Mark-MDO47/GraduationCap2017/Buttons/images/71s4Z-NuidL._SL1500_.jpg

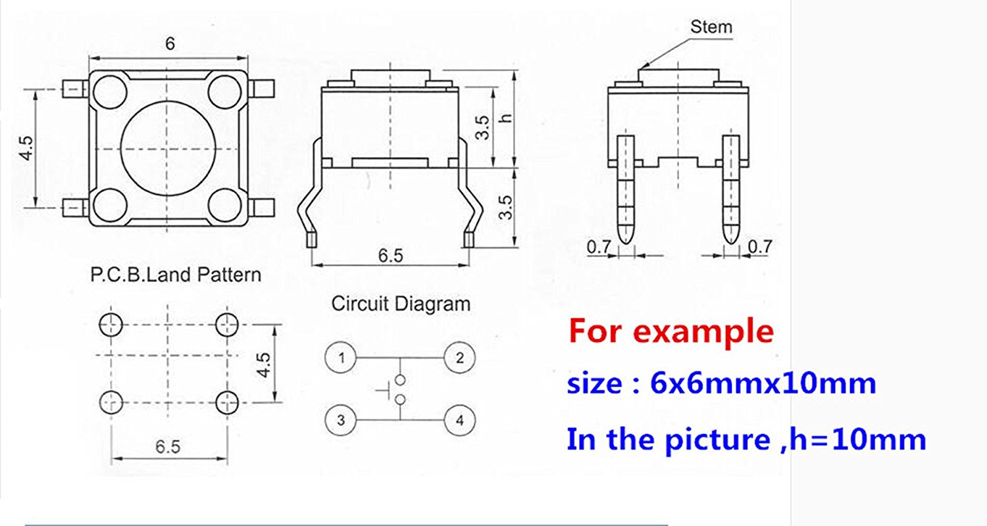
Buttons/images/71s4Z-NuidL._SL1500_.jpg
