Mark-MDO47/GraduationCap2017/FirstCap/GradCapWithDisks_FirstAttempt.JPG

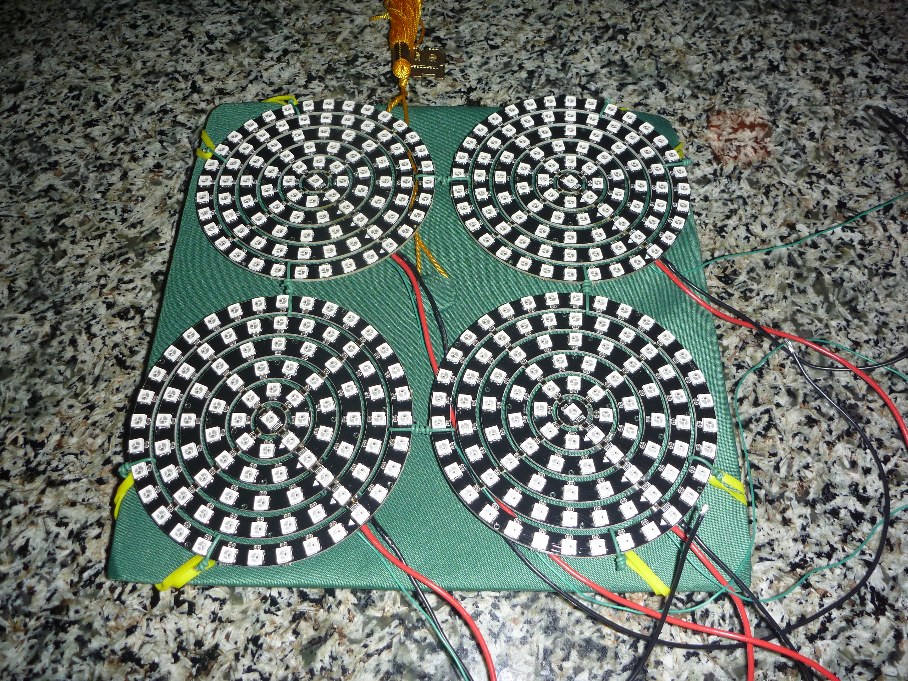
FirstCap/GradCapWithDisks_FirstAttempt.JPG
