Mark-MDO47/GraduationCap2017/FirstCap/P1010498.JPG

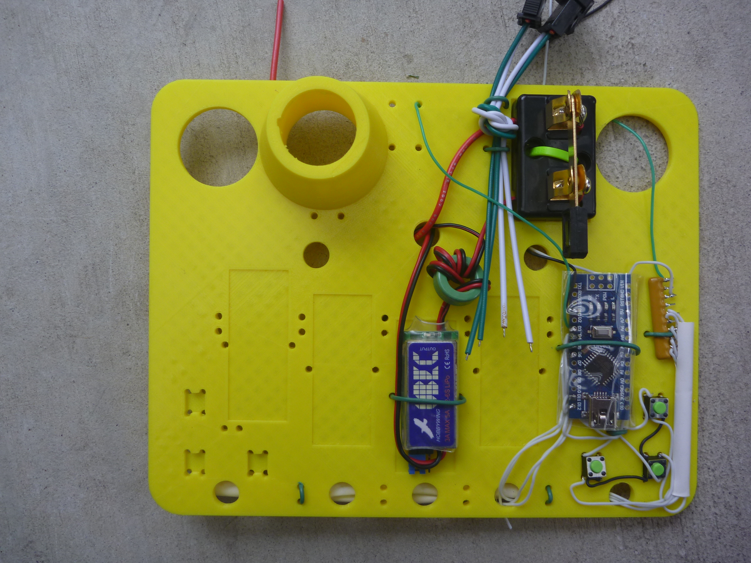
FirstCap/P1010498.JPG
