Mark-MDO47/GraduationCap2017/FirstCap/P1010499.JPG

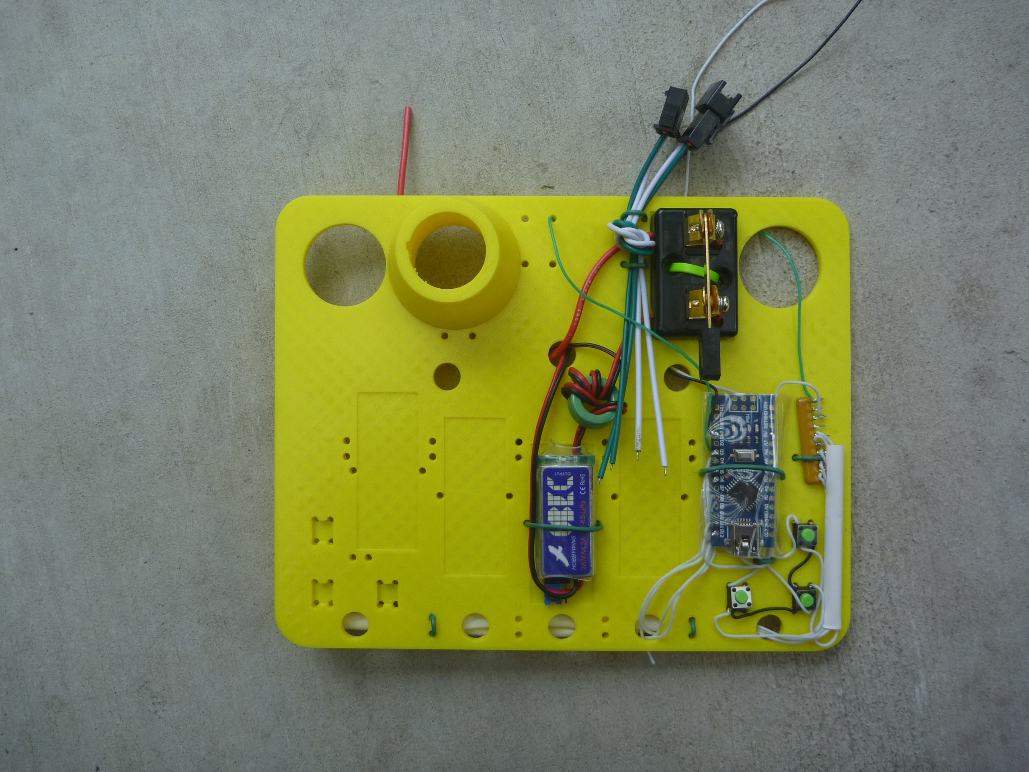
FirstCap/P1010499.JPG
