Mark-MDO47/GraduationCap2017/FirstCap/P1010500.JPG

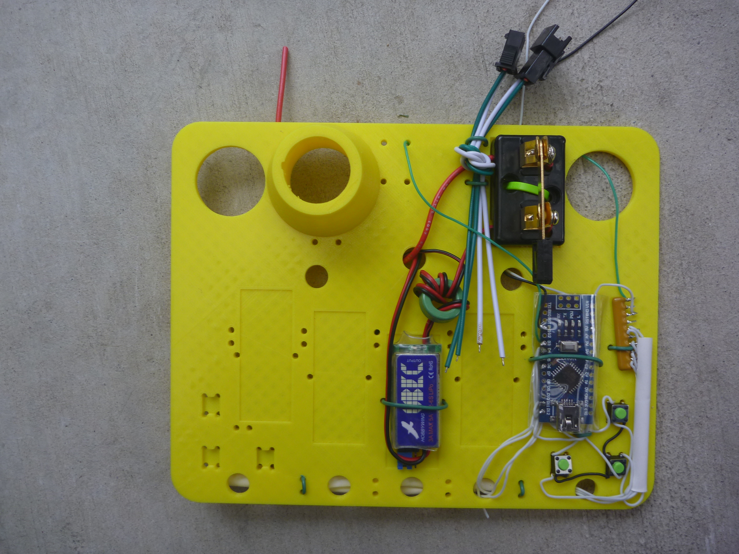
FirstCap/P1010500.JPG
