Mark-MDO47/GraduationCap2017/FirstCap/P1010501.JPG

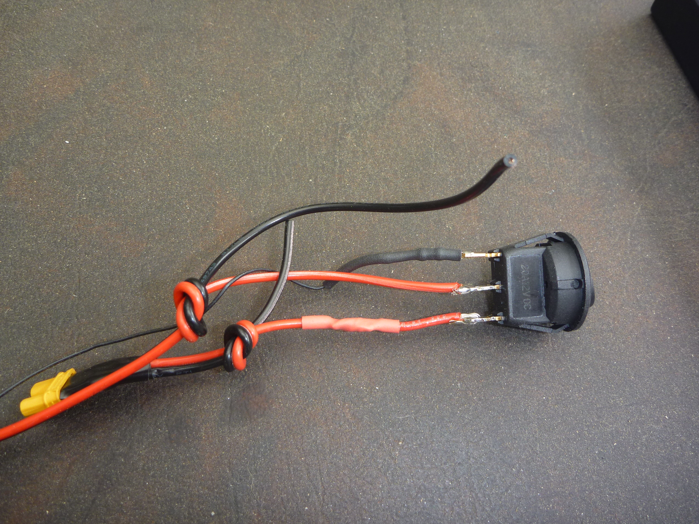
FirstCap/P1010501.JPG
