Mark-MDO47/GraduationCap2017/FirstCap/P1010502.JPG

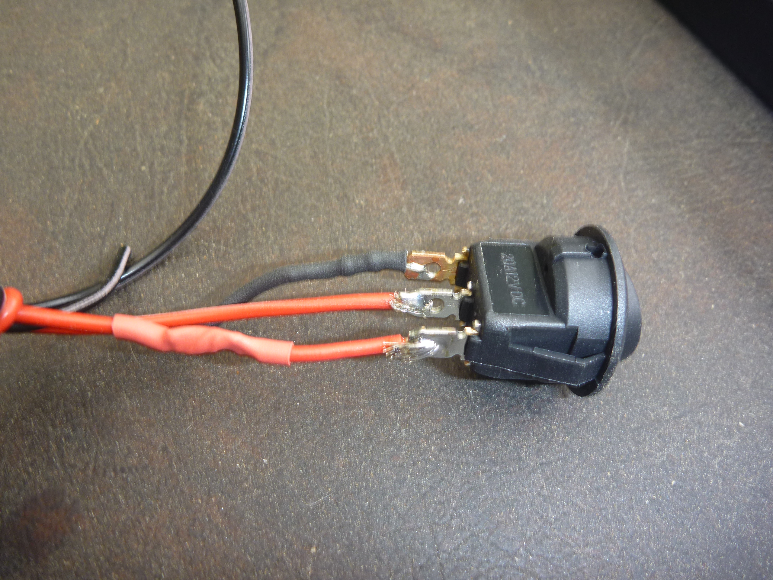
FirstCap/P1010502.JPG
