Mark-MDO47/GraduationCap2017/FirstCap/P1010503.JPG

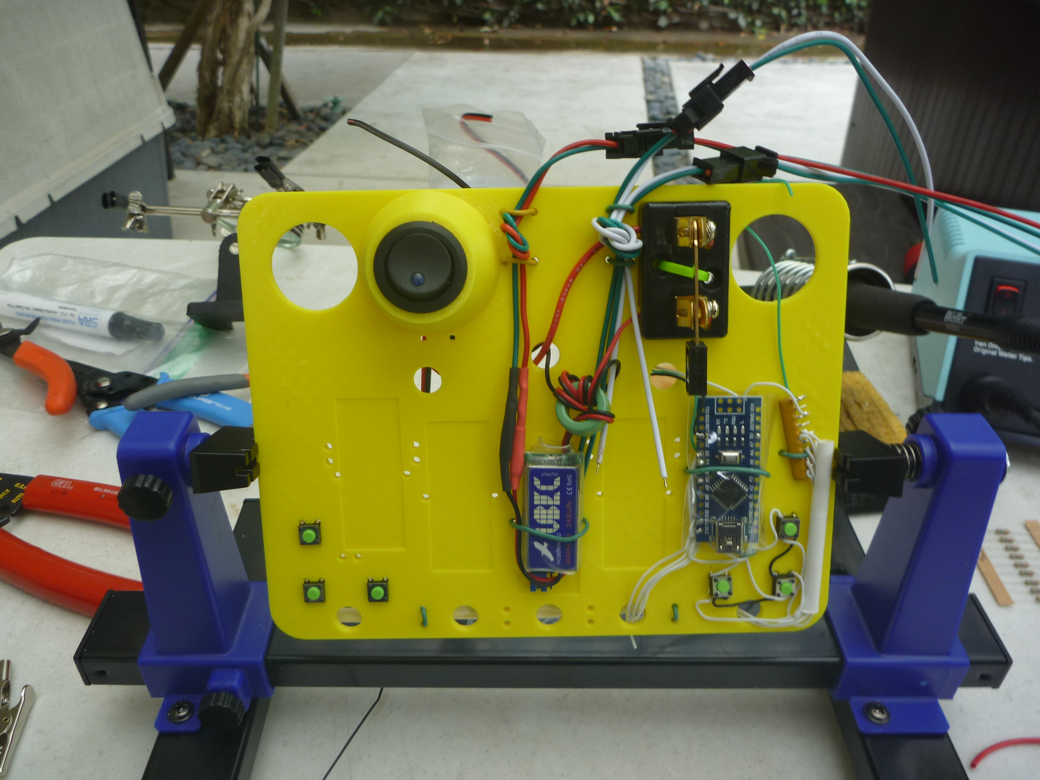
FirstCap/P1010503.JPG
