Mark-MDO47/GraduationCap2017/FirstCap/P1010506.JPG

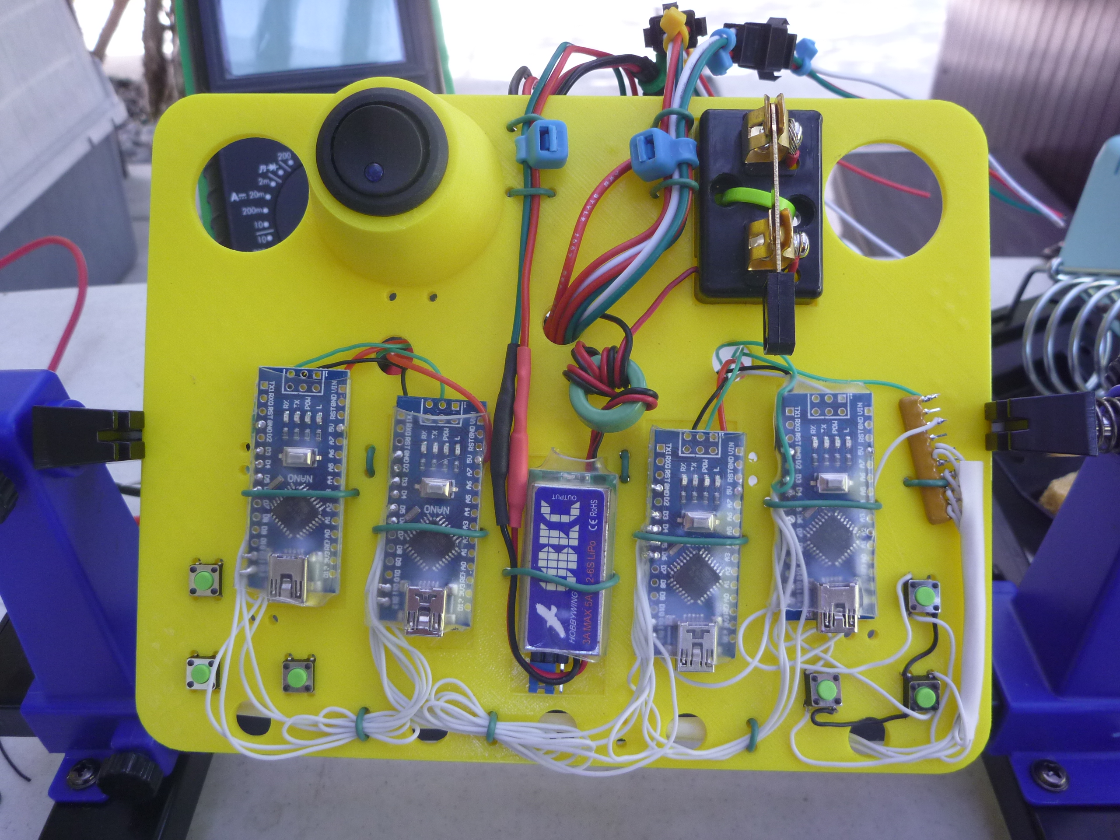
FirstCap/P1010506.JPG
