Mark-MDO47/GraduationCap2017/FirstCap/P1010507.JPG

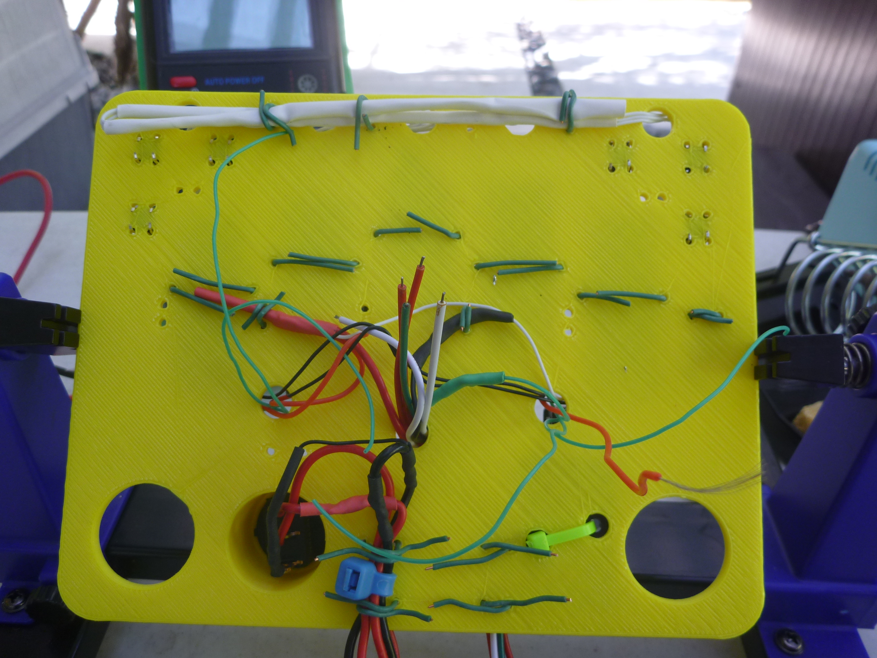
FirstCap/P1010507.JPG
