Mark-MDO47/GraduationCap2017/FirstCap/P1010508.JPG

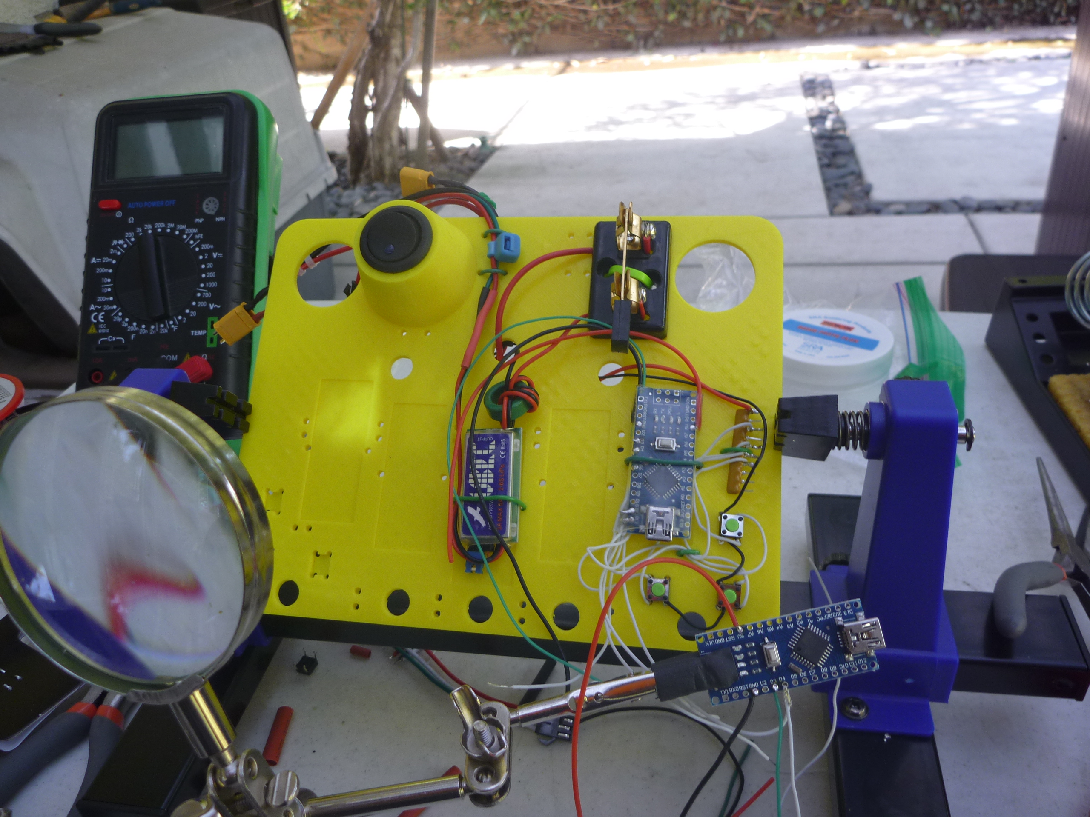
FirstCap/P1010508.JPG
