Mark-MDO47/GraduationCap2017/FirstCap/P1010509.JPG

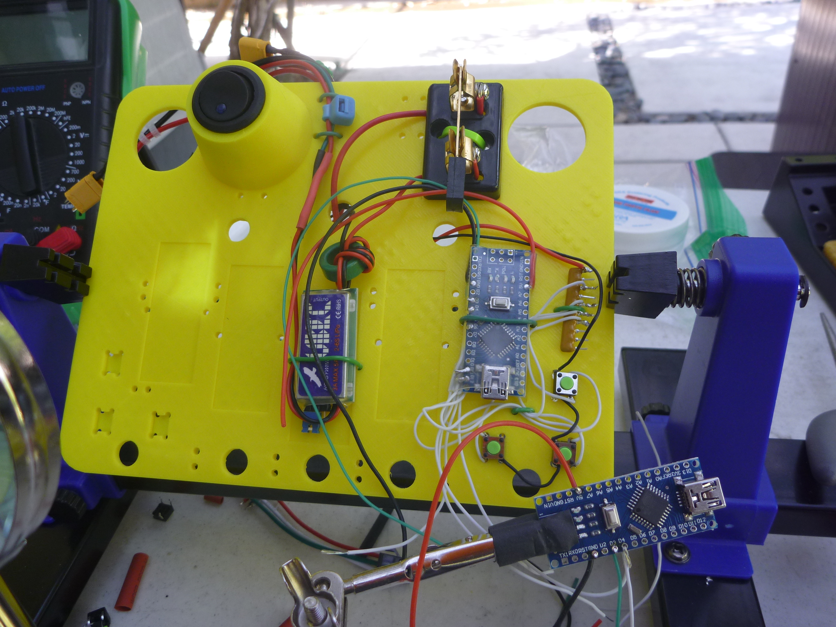
FirstCap/P1010509.JPG
