Mark-MDO47/GraduationCap2017/FirstCap/P1010510.JPG

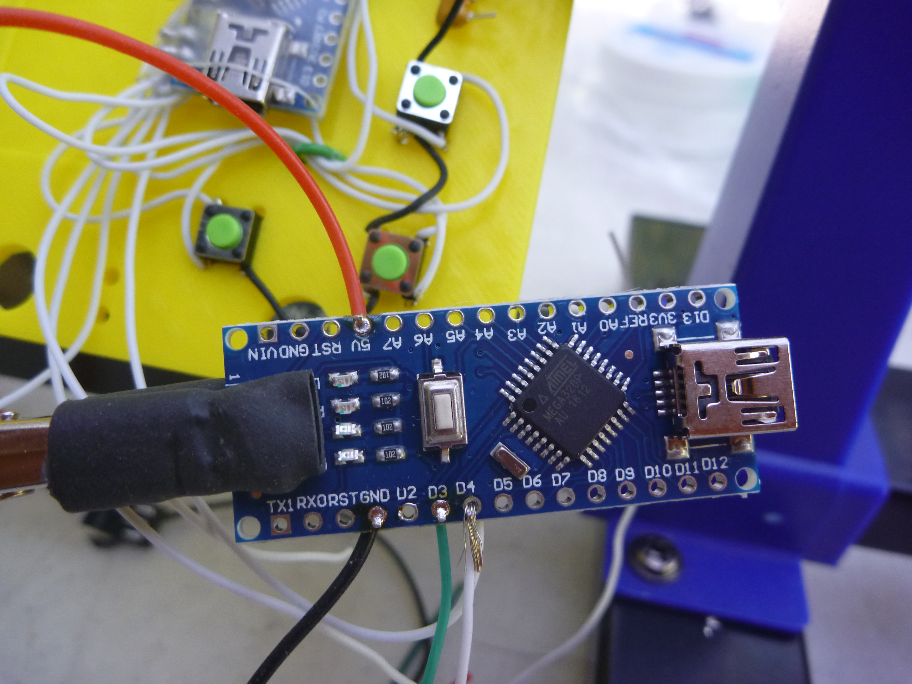
FirstCap/P1010510.JPG
