Mark-MDO47/GraduationCap2017/FirstCap/P1010511.JPG

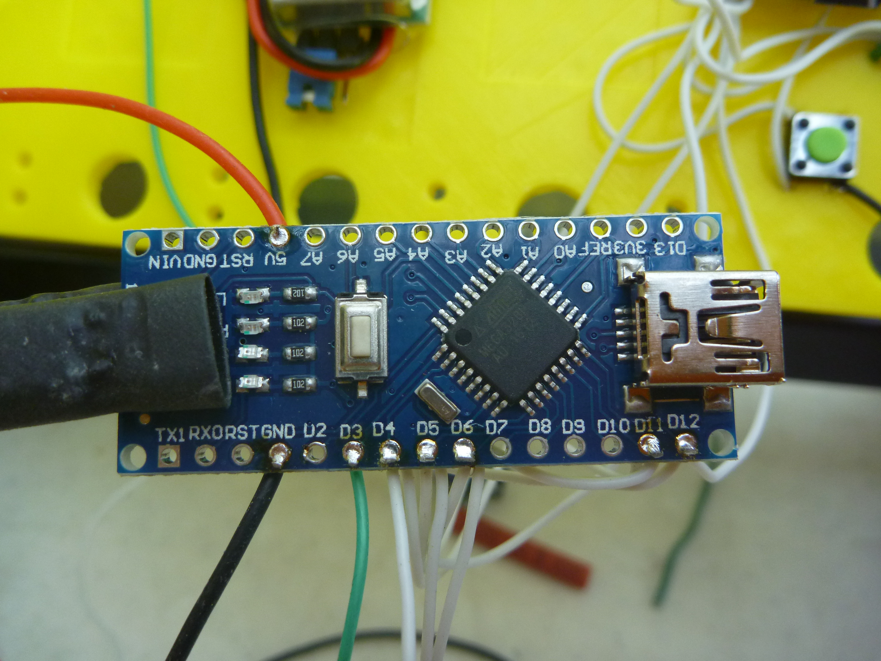
FirstCap/P1010511.JPG
