Mark-MDO47/GraduationCap2017/FirstCap/P1010512.JPG

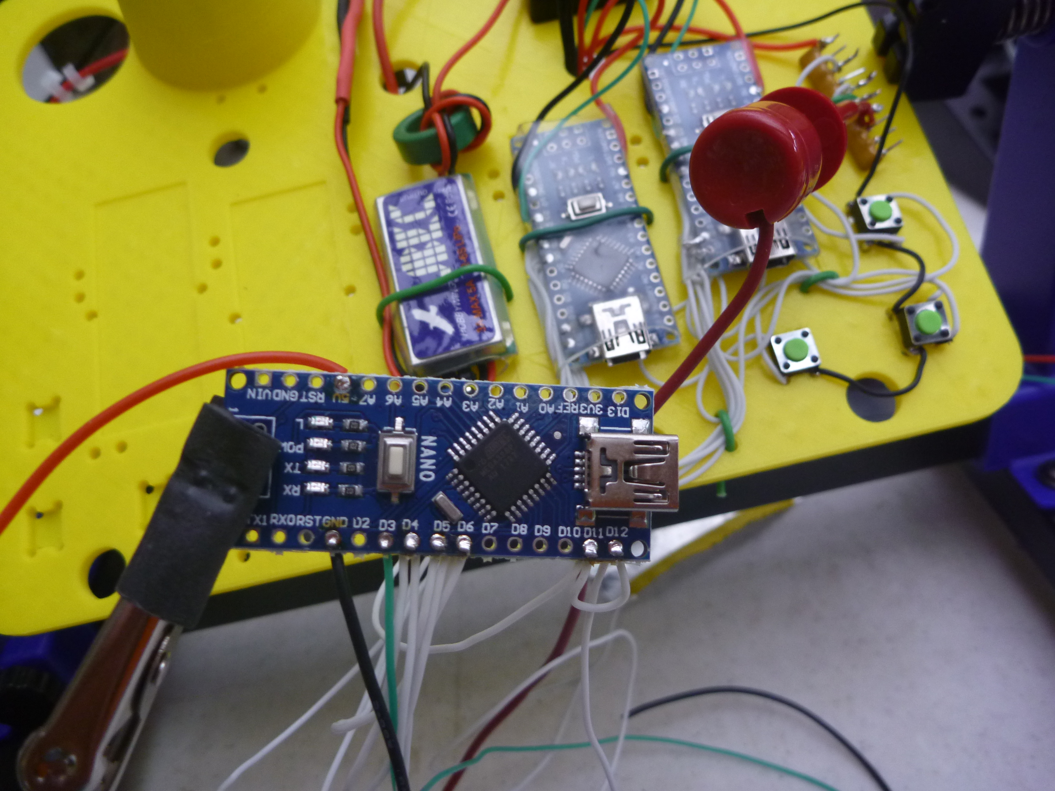
FirstCap/P1010512.JPG
