Mark-MDO47/GraduationCap2017/FirstCap/P1010513.JPG

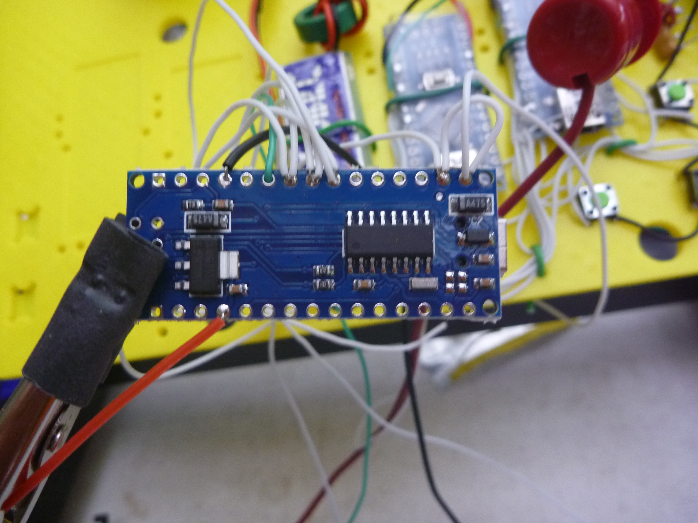
FirstCap/P1010513.JPG
