Mark-MDO47/GraduationCap2017/imagesFinal/IMG_09512_controller_purse.png

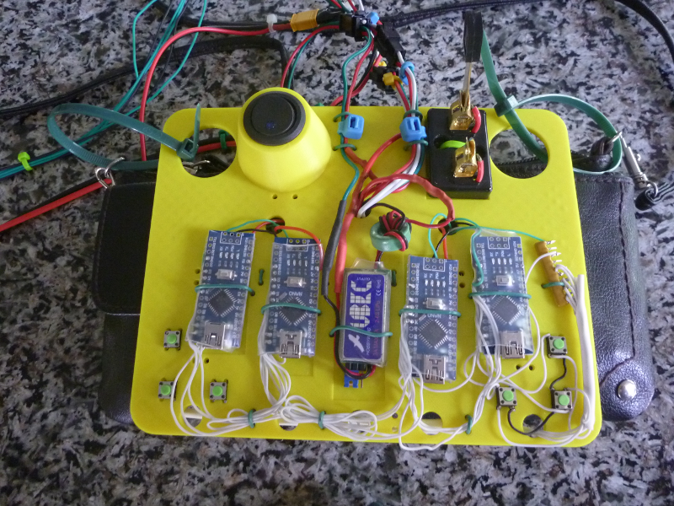
imagesFinal/IMG_09512_controller_purse.png
