Mark-MDO47/GraduationCap2017/imagesFinal/IMG_09513_cap.png

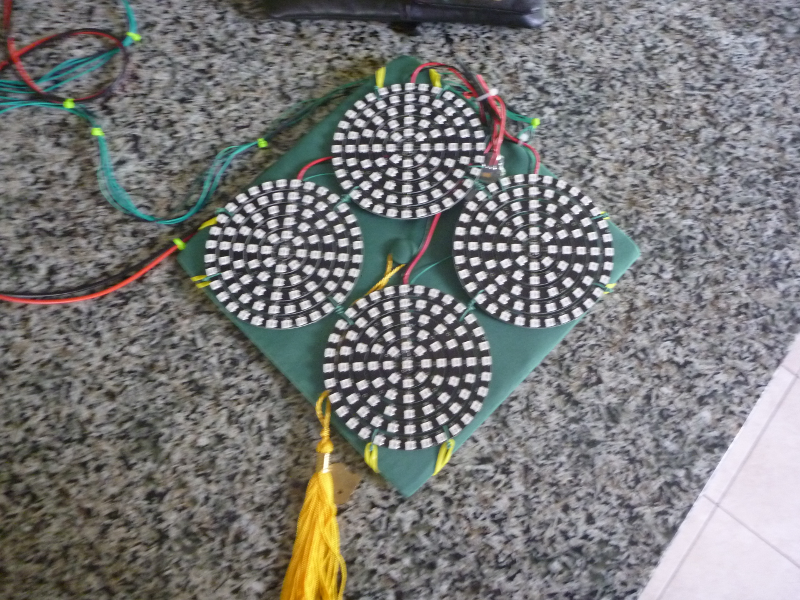
imagesFinal/IMG_09513_cap.png
