Mark-MDO47/GraduationCap2017/3D-Print/GradCapPurseHanger_2D_boardonly.png

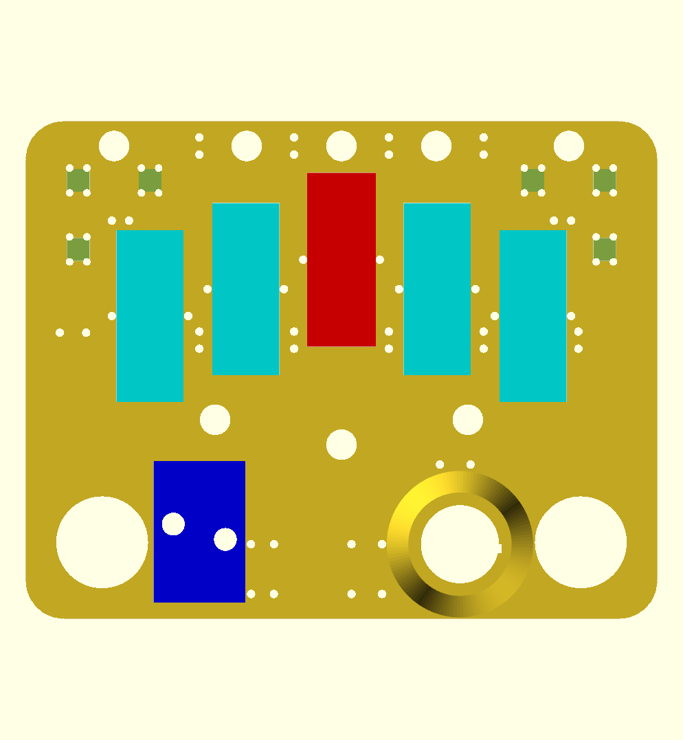
3D-Print/GradCapPurseHanger_2D_boardonly.png
