Mark-MDO47/GraduationCap2017/3D-Print/GradCapPurseHanger_3D.png

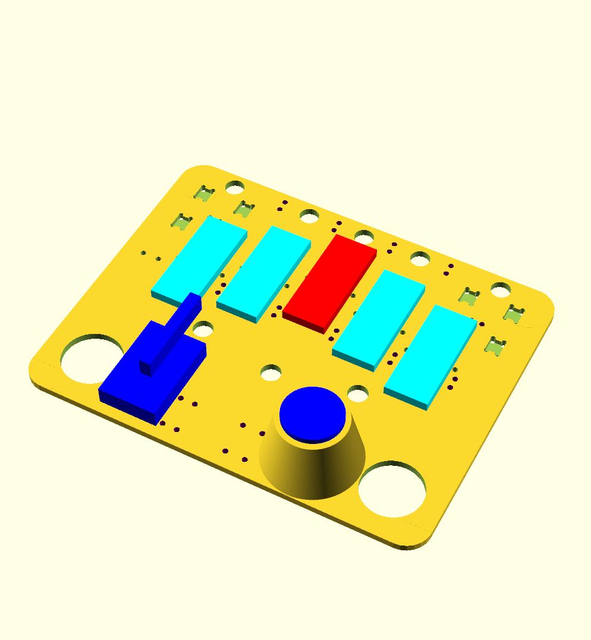
3D-Print/GradCapPurseHanger_3D.png
