Mark-MDO47/GraduationCap2017/3D-Print/GradCapPurseHanger_3D_boardonly.png

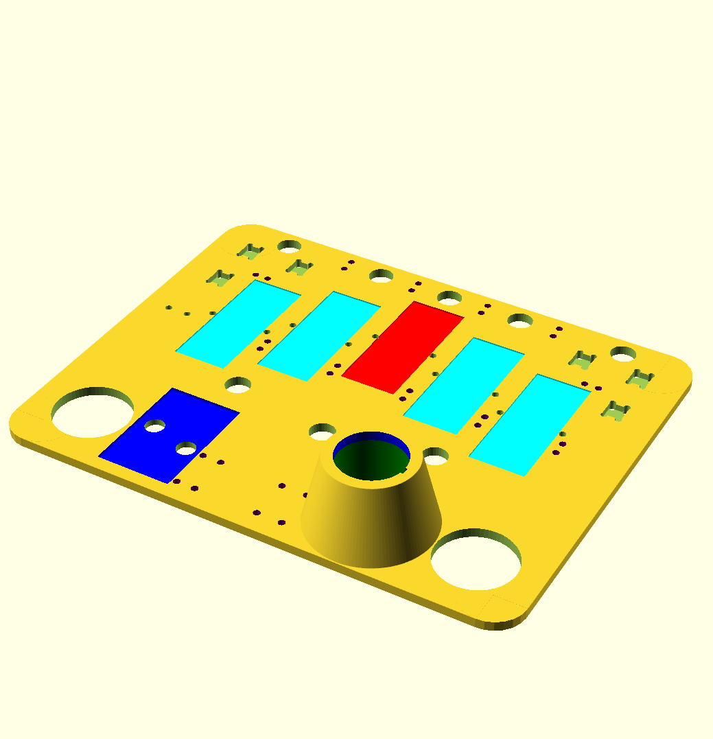
3D-Print/GradCapPurseHanger_3D_boardonly.png
