Mark-MDO47/GraduationCap2017/3D-Print/Oops/2018-05-06/P1010493.JPG

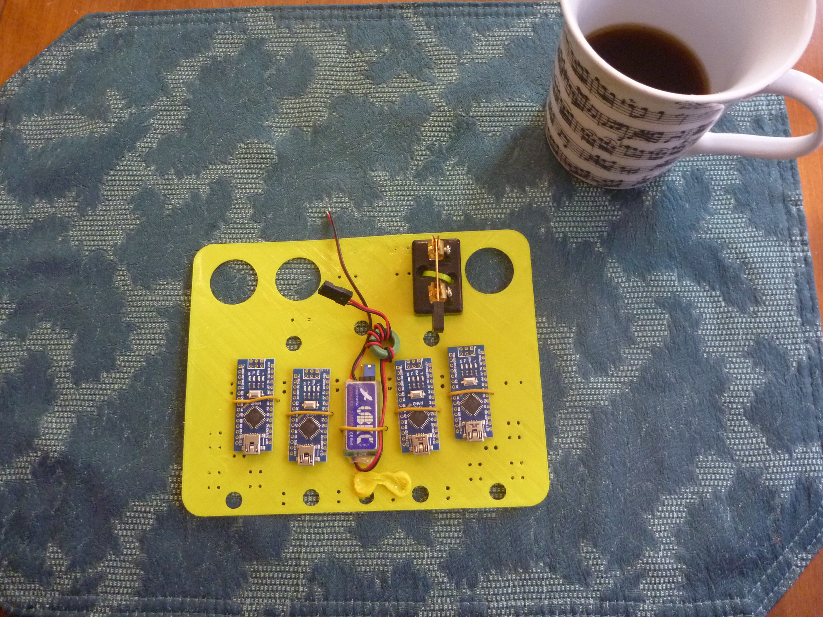
3D-Print/Oops/2018-05-06/P1010493.JPG
