Mark-MDO47/GraduationCap2017/buildInfo/CapTopView.png

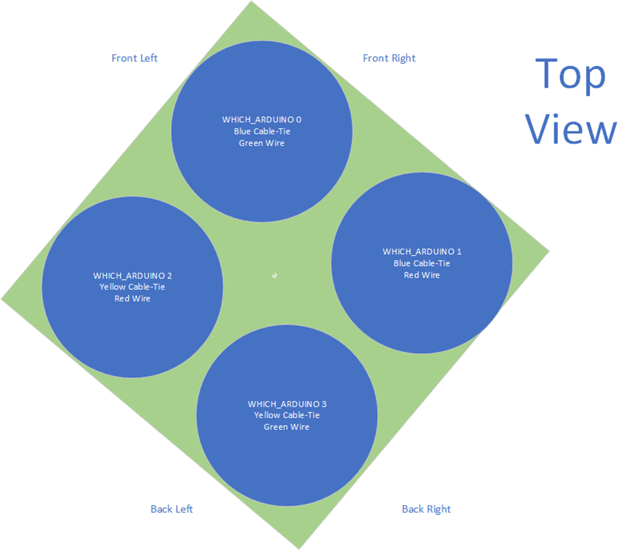
buildInfo/CapTopView.png
