Mark-MDO47/GraduationCap2017/buildInfo/WS2812B_Disk_Wiring.png

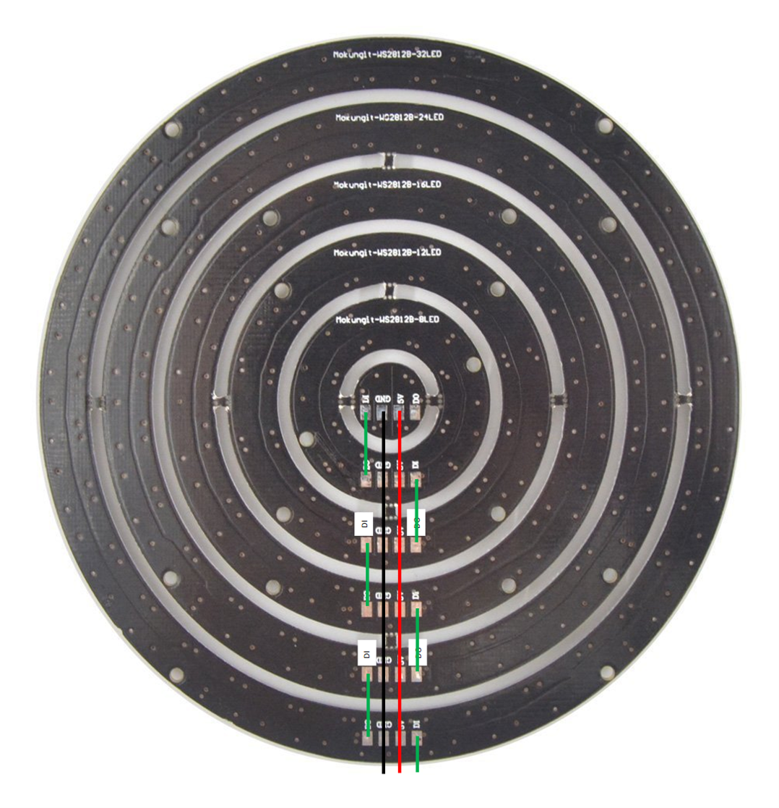
buildInfo/WS2812B_Disk_Wiring.png
