Mark-MDO47/GraduationCap2017/FirstCap/LED_Disk_soldering_closeup.JPG

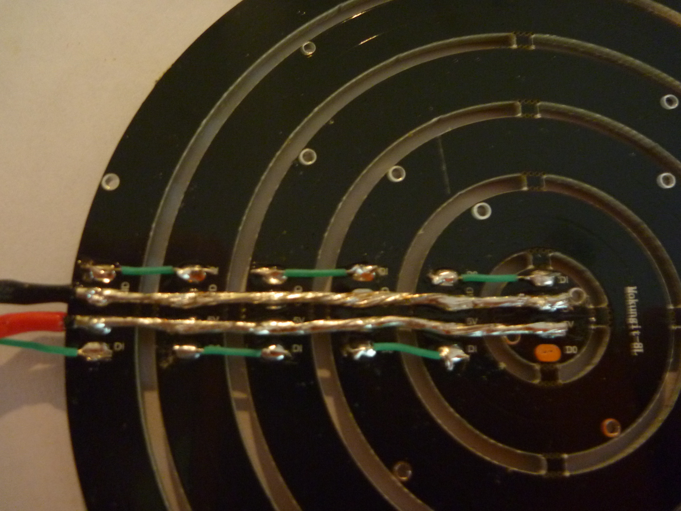
FirstCap/LED_Disk_soldering_closeup.JPG
